AllenNeuralDynamics/harp.device.cuttlefish/firmware/src/cuttlefish_app.cpp

#include <cuttlefish_app.h>

app_regs_t app_regs;

// Define "specs" per-register
RegSpec app_reg_specs[]
{
    RegSpec::U8(&app_regs.port_dir,
        Harp::read_reg_generic, write_port_dir),
    RegSpec::U8(&app_regs.port_state,
        read_port_state, write_port_state),
    RegSpec::U8(&app_regs.port_set,
        Harp::read_reg_error, write_port_set),
    RegSpec::U8(&app_regs.port_clear,
        Harp::read_reg_error, write_port_clear),
    RegSpec::U8(&app_regs.enable_rising_edge_events,
        Harp::read_reg_generic, write_enable_rising_edge_events),
    RegSpec::U8(&app_regs.rising_edge_events,
        Harp::read_reg_error, Harp::write_reg_error),
    RegSpec::U8(&app_regs.enable_falling_edge_events,
        Harp::read_reg_generic, write_enable_falling_edge_events),
    RegSpec::U8(&app_regs.falling_edge_events,
        Harp::read_reg_error, Harp::write_reg_error),
    RegSpec::U8(&app_regs.pwm_state,
        Harp::read_reg_generic, write_pwm_state),
    RegSpec::U8Array(&app_regs.pwm_settings[0], sizeof(pwm_settings_t),
        Harp::read_reg_generic, write_any_pwm_settings),
    RegSpec::U8Array(&app_regs.pwm_settings[1], sizeof(pwm_settings_t),
        Harp::read_reg_generic, write_any_pwm_settings),
    RegSpec::U8Array(&app_regs.pwm_settings[2], sizeof(pwm_settings_t),
        Harp::read_reg_generic, write_any_pwm_settings),
    RegSpec::U8Array(&app_regs.pwm_settings[3], sizeof(pwm_settings_t),
        Harp::read_reg_generic, write_any_pwm_settings),
    RegSpec::U8Array(&app_regs.pwm_settings[4], sizeof(pwm_settings_t),
        Harp::read_reg_generic, write_any_pwm_settings),
    RegSpec::U8Array(&app_regs.pwm_settings[5], sizeof(pwm_settings_t),
        Harp::read_reg_generic, write_any_pwm_settings),
    RegSpec::U8Array(&app_regs.pwm_settings[6], sizeof(pwm_settings_t),
        Harp::read_reg_generic, write_any_pwm_settings),
    RegSpec::U8Array(&app_regs.pwm_settings[7], sizeof(pwm_settings_t),
        Harp::read_reg_generic, write_any_pwm_settings)
};

const size_t APP_REG_COUNT = sizeof(app_reg_specs) / sizeof(RegSpec);

inline void set_io_port_dir(uint8_t port_dir)
{
    // Set both buffer ctrl pins and corresponding IO pins to match.
    // Omit setting direction of pins used by existing PWM Tasks.
    gpio_put_masked(PORT_DIR_MASK, uint32_t(port_dir) << PORT_DIR_BASE);
    gpio_set_dir_masked(PORT_MASK, uint32_t(port_dir) << PORT_BASE);
}

void write_port_dir(msg_t& msg)
{
    Harp::copy_msg_payload_to_register(msg);
    set_io_port_dir(app_regs.port_dir);
    if (!Harp::is_muted())
        Harp::send_harp_reply(WRITE, msg.header.address);
}


void read_port_state(uint8_t reg_address)
{
    // Include the state of pins driven by PWMTasks.
    app_regs.port_state = uint8_t(gpio_get_all() >> PORT_BASE);
    if (!Harp::is_muted())
        Harp::send_harp_reply(READ, reg_address);
}


void write_port_state(msg_t& msg)
{
    Harp::copy_msg_payload_to_register(msg);
    // write to output pins
    gpio_put_masked(uint32_t(app_regs.port_dir) << PORT_BASE,
                    uint32_t(app_regs.port_state) << PORT_BASE);
    // Read back what we just wrote since it's fast.
    // Add delay for change to take effect. (May be related to slew rate).
    asm volatile("nop \n nop \n nop");
    app_regs.port_state = uint8_t(gpio_get_all() >> PORT_BASE);
    if (!Harp::is_muted())
        Harp::send_harp_reply(WRITE, msg.header.address);
}


void write_port_set(msg_t& msg)
{
    Harp::copy_msg_payload_to_register(msg);
    gpio_put_masked(uint32_t(app_regs.port_set) << PORT_BASE,
                    uint32_t(app_regs.port_set) << PORT_BASE);
    if (!Harp::is_muted())
        Harp::send_harp_reply(WRITE, msg.header.address);
}


void write_port_clear(msg_t& msg)
{
    Harp::copy_msg_payload_to_register(msg);
    gpio_put_masked(uint32_t(app_regs.port_clear) << PORT_BASE, 0);
    if (!Harp::is_muted())
        Harp::send_harp_reply(WRITE, msg.header.address);
}


void write_enable_rising_edge_events(msg_t& msg)
{
    Harp::copy_msg_payload_to_register(msg);
    for (size_t i = 0; i < NUM_GPIOS; ++i)
    {
        bool enabled = ((app_regs.enable_rising_edge_events >> i) & 1u);
        gpio_set_irq_enabled(i + PORT_BASE, GPIO_IRQ_EDGE_RISE, enabled);
    }
    if (!Harp::is_muted())
        Harp::send_harp_reply(WRITE, msg.header.address);
}




void write_enable_falling_edge_events(msg_t& msg)
{
    Harp::copy_msg_payload_to_register(msg);
    for (size_t i = 0; i < NUM_GPIOS; ++i)
    {
        bool enabled = ((app_regs.enable_falling_edge_events >> i) & 1u);
        gpio_set_irq_enabled(i + PORT_BASE, GPIO_IRQ_EDGE_FALL, enabled);
    }
    if (!Harp::is_muted())
        Harp::send_harp_reply(WRITE, msg.header.address);
}


void write_pwm_state(msg_t& msg)
{
    using enum pwm_ctrl_msg_t;
    uint8_t old_state = app_regs.pwm_state;
    Harp::copy_msg_payload_to_register(msg);
    uint8_t& new_state = app_regs.pwm_state;
    // Error if we are already running.
    if (((old_state > 0) && (new_state > 0)))
    {
        if (!Harp::is_muted())
            Harp::send_harp_reply(WRITE_ERROR, msg.header.address);
        return;
    }
    // Ignore repeats of the same "clear" command and don't flag it as an error.
    if (((old_state == 0) && (new_state == 0)))
    {
        if (!Harp::is_muted())
            Harp::send_harp_reply(WRITE, msg.header.address);
        return;
    }
    // Error if we have never specified any PWM Settings
    if (!app_regs.pwm_ready)
    {
        if (!Harp::is_muted())
            Harp::send_harp_reply(WRITE_ERROR, msg.header.address);
        return;
    }
    // Send Core1 message to start the schedule.
    pwm_ctrl_msg_t ctrl_msg = (new_state > 0) ? START: STOP;
    queue_try_add(&core1_ctrl_queue, &ctrl_msg);
    // Wait (but not that long) for Core1 to indicate when it started.
    core1_next_state_msg_t state_change_msg;
    uint32_t start_time_us = time_us_32_fast();
    while (int(time_us_32_fast() - start_time_us) < INTERCORE_COM_TIMEOUT_US)
    {
        if (!queue_try_remove(&core1_next_state_queue, &state_change_msg))
            continue;
        if (Harp::is_muted())
            return;
        // Deduce outcome success / failure.
        // Cmd stop & result stop (ready) ? --> success
        // Cmd start & result running ? --> success
        msg_type_t harp_reply_type = WRITE_ERROR;
        if (new_state > 0 && state_change_msg.next_state == core1_state_t::RUNNING)
            harp_reply_type = WRITE;
        if (new_state == 0 && state_change_msg.next_state == core1_state_t::READY)
            harp_reply_type = WRITE;
        Harp::send_harp_reply(harp_reply_type, msg.header.address,
            Harp::system_to_harp_us_64(state_change_msg.timestamp_us));
        return;
    }
    // Error if made it this far (timed out). Core1 unresponsive?
    if (!Harp::is_muted())
        Harp::send_harp_reply(WRITE_ERROR, msg.header.address);
}


void write_any_pwm_settings(msg_t& msg)
{
    // Error if core1 is busy.
    if (app_regs.pwm_state)
    {
        if (!Harp::is_muted())
            Harp::send_harp_reply(WRITE_ERROR, msg.header.address);
        return;
    }
    Harp::copy_msg_payload_to_register(msg);
    // Backtrack both data and index in the corresponding array it belongs to.
    const RegSpec& spec = Harp::reg_address_to_spec(msg.header.address);
    pwm_settings_t& pwm_settings = *((pwm_settings_t*)spec.base_ptr);
    size_t pwm_index = &pwm_settings - app_regs.pwm_settings; // subtract ptrs.
    // Record that this pwm pin is now armed.
    app_regs.pwm_ready |= 1u << pwm_index;
    // Mark pin as OUTPUT in app registers and update buffer ctrl pin to match.
    app_regs.port_dir |= 1u << pwm_index;
    set_io_port_dir(app_regs.port_dir);
    // Push new pwm settings to core1.
    size_t pwm_pin = pwm_index + PORT_BASE;
    pwm_specs_core_msg_t pwm_msg(pwm_pin, pwm_settings);
    if (!queue_try_add(&pwm_settings_queue, &pwm_msg))
    {
        if (!Harp::is_muted())
            Harp::send_harp_reply(WRITE_ERROR, msg.header.address);
        return;
    }
    // Set buffer ctrl pins to drive an output to passthrough PWM signal.
    uint32_t buffer_mask = 1u << (PORT_DIR_BASE + pwm_index);
    gpio_put_masked(buffer_mask, 0xFFFFFFFF);
    // Finish write transaction successfully.
    if (!Harp::is_muted())
        Harp::send_harp_reply(WRITE, msg.header.address);
}


void handle_edge_event_callback(void)
{
    // FYI raw interrupt state for all 30 GPIOs is split across 4 registers
    // (INTR0, ..., INTR3).
    // Since Cuttlefish only has 8 consecutive GPIOS offset by a multiple of 8,
    // we can get away with doing a single register read to access the entire
    // interrupt state (rising, falling, high low) for the 8 pins of interest.
    EdgeEvent event;
    event.timestamp_us = time_us_64(); // ISR safe.
    event.rise_pins = 0;
    event.fall_pins = 0;
    uint32_t intr_state = io_bank0_hw->intr[PORT_BASE >> 3];
    uint32_t gpio_flags;
    // Split up rising/falling edge events.
    for (size_t i = 0; i < NUM_GPIOS; ++i)
    {
        gpio_flags = intr_state >> (i * 4); // 4 flags per gpio pin.
        event.rise_pins |= (((gpio_flags >> 3) & 1u) << i + PORT_BASE);
        event.fall_pins |= (((gpio_flags >> 2) & 1u) << i + PORT_BASE);
    }
    // Push the event
    queue_try_add(&edge_event_queue, &event);
    // Clear the INTR[n] state since we dealt with all pin changes.
    // Clear by "writing a 1" to the set bits.
    io_bank0_hw->intr[PORT_BASE >> 3] = 0xFFFFFFFF; // >> 3: floor-divide by 8
}


void update_app_state()
{
    // Check for pin state changes pushed to edge event queue.
    // Drain queue. Warn if pin change rate is too fast.
    EdgeEvent event;
    while (queue_try_remove(&edge_event_queue, &event))
    {
        if (Harp::is_muted())
            continue;
        // Copy to EVENT-only register and filter for enabled pins.
        app_regs.rising_edge_events = uint8_t(event.rise_pins >> PORT_BASE) &
                                       app_regs.enable_rising_edge_events;
        app_regs.falling_edge_events = uint8_t(event.fall_pins >> PORT_BASE) &
                                        app_regs.enable_falling_edge_events;
        // Push queued messages from rising or falling edge events register.
        if (app_regs.rising_edge_events)
        {
            uint64_t harp_time_us = Harp::system_to_harp_us_64(event.timestamp_us);
            Harp::send_harp_reply(EVENT, RISING_EDGE_EVENTS_ADDRESS, harp_time_us);
        }
        if (app_regs.falling_edge_events) // filter
        {
            uint64_t harp_time_us = Harp::system_to_harp_us_64(event.timestamp_us);
            Harp::send_harp_reply(EVENT, FALLING_EDGE_EVENTS_ADDRESS, harp_time_us);
        }
    }
    // Update local state if core1 finished and send EVENT message.
    core1_next_state_msg_t state_change_msg;
    if (!queue_try_remove(&core1_next_state_queue, &state_change_msg))
        return;
    // Clear local pwm registers and send back a reply if the schedule finishes
    // without being stopped via external Harp command.
    if (state_change_msg.next_state == core1_state_t::RESET)
    {
        app_regs.pwm_ready = 0;
        app_regs.pwm_state = 0; // "finished"
    }
    else if (state_change_msg.next_state == core1_state_t::READY)
    {
        app_regs.pwm_state = 0; // "finished"
        Harp::send_harp_reply(EVENT, PWM_STATE_ADDRESS,
                              state_change_msg.timestamp_us);
    }
}

void reset_app()
{
    // TODO: send core1 signal to stop?
    // TODO: reset core1 before resetting GPIO state.

    // Drain all inter-core communication queues.
    core1_next_state_msg_t  dummy_next_state_msg;
    while (queue_try_remove(&core1_next_state_queue, &dummy_next_state_msg)) {}
    pwm_ctrl_msg_t dummy_ctrl_msg;
    while (queue_try_remove(&core1_ctrl_queue, &dummy_ctrl_msg)) {}
    pwm_specs_core_msg_t dummy_pwm_settings;
    while (queue_try_remove(&pwm_settings_queue, &dummy_pwm_settings)) {}

    // init all pins used as GPIOs.
    gpio_init_mask(PORT_MASK | PORT_DIR_MASK);
    // Reset unbuffered IO pins to inputs.
    gpio_set_dir_masked(PORT_MASK, 0);
    // Reset Buffer ctrl pins to all outputs and drive an input setting.
    gpio_set_dir_masked(PORT_DIR_MASK, 0xFFFFFFFF);
    gpio_put_masked(PORT_DIR_MASK, 0);
    // Reset Harp register struct elements.
    app_regs.port_dir = 0x00; // all inputs
    app_regs.port_state = uint8_t(gpio_get_all() >> PORT_BASE);
    app_regs.pwm_state = 0;
    app_regs.pwm_ready = 0;
    for (size_t i = 0; i < NUM_GPIOS; ++i)
        app_regs.pwm_settings[i] = pwm_settings_t();

    // Drain the EdgeEvent queue.
    EdgeEvent dummy_event;
    while (queue_try_remove(&edge_event_queue, &dummy_event)) {}
    // Detach any existing interrupt handlers.
    for (size_t i = 0; i < NUM_GPIOS; ++i)
        gpio_set_irq_enabled(i + PORT_BASE,
                             GPIO_IRQ_EDGE_RISE | GPIO_IRQ_EDGE_FALL, false);
    // Attach interrupt handlers.
    irq_add_shared_handler(IO_IRQ_BANK0, handle_edge_event_callback,
                           GPIO_IRQ_CALLBACK_ORDER_PRIORITY);
    irq_set_enabled(IO_IRQ_BANK0, true);
}
